AESilky/scores/src/panel/panel_msg_hndlr.h

/**
 * Scoreboard Panel Message Handlers.
 *
 * Copyright 2023 AESilky
 * SPDX-License-Identifier: MIT License
 *
*/
#ifndef _SCORE_PANEL_MH_H_
#define _SCORE_PANEL_MH_H_
#ifdef __cplusplus
extern "C" {
#endif
#include "cmt/cmt.h"

extern const msg_handler_entry_t _panel_slowblnk_handler_entry;

#ifdef __cplusplus
}
#endif
#endif // _SCORE_PANEL_MH_H_
